vpalaga/DrawMachine/StepperDriver-pico/drivers/StepperDriver.h

#ifndef STEPPERDRIVER_H
#define STEPPERDRIVER_H

#include "Stepper.h"
class StepperDriver {
public:
    int motor_sleep_us;
    
    bool x_dir;
    bool y_dir;

    StepperDriver(Stepper::stepper_pins pins_x, Stepper::stepper_pins pins_y);
    void move(int x, int y);
    void bresenham(Stepper leadStepper, Stepper followStepper, int lead, int follow, bool leadDir, bool followDir);
    void enable(bool setState);
    void pos_reset();
    void printPosToTermial();

    int x_pos = 0;
    int y_pos = 0;
    bool is_pen_down = false;

private:
    Stepper xStepperMotor;
    Stepper yStepperMotor;

    int USE_SPROFILE_FROM_STEPS;
    double MM_p_STEP;
    

};

#endif
